trwgQ26xxx/LED_clock/FRAME/FRONT_STICKER/STICKER_CUT_3.pdf

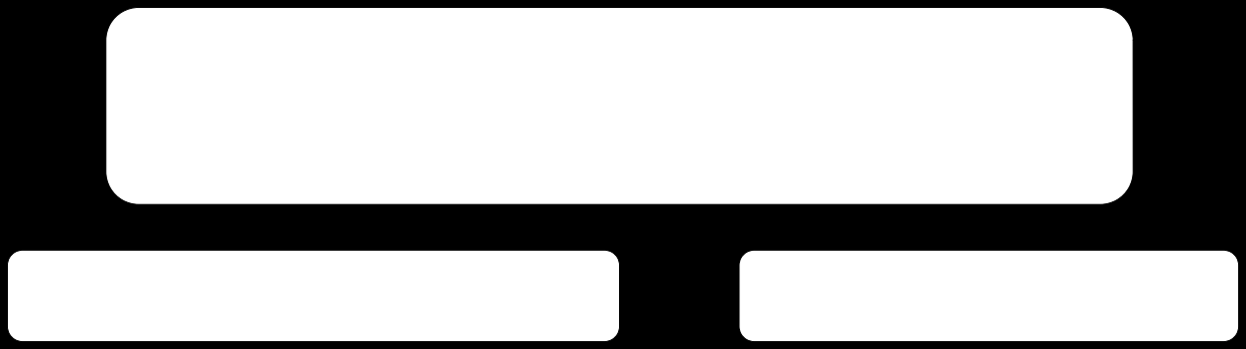
[picture p2: figure]
