trwgQ26xxx/LED_clock/FRAME/MOUNTING_PLATE/PLATE_WITH_DIMENSIONS.pdf

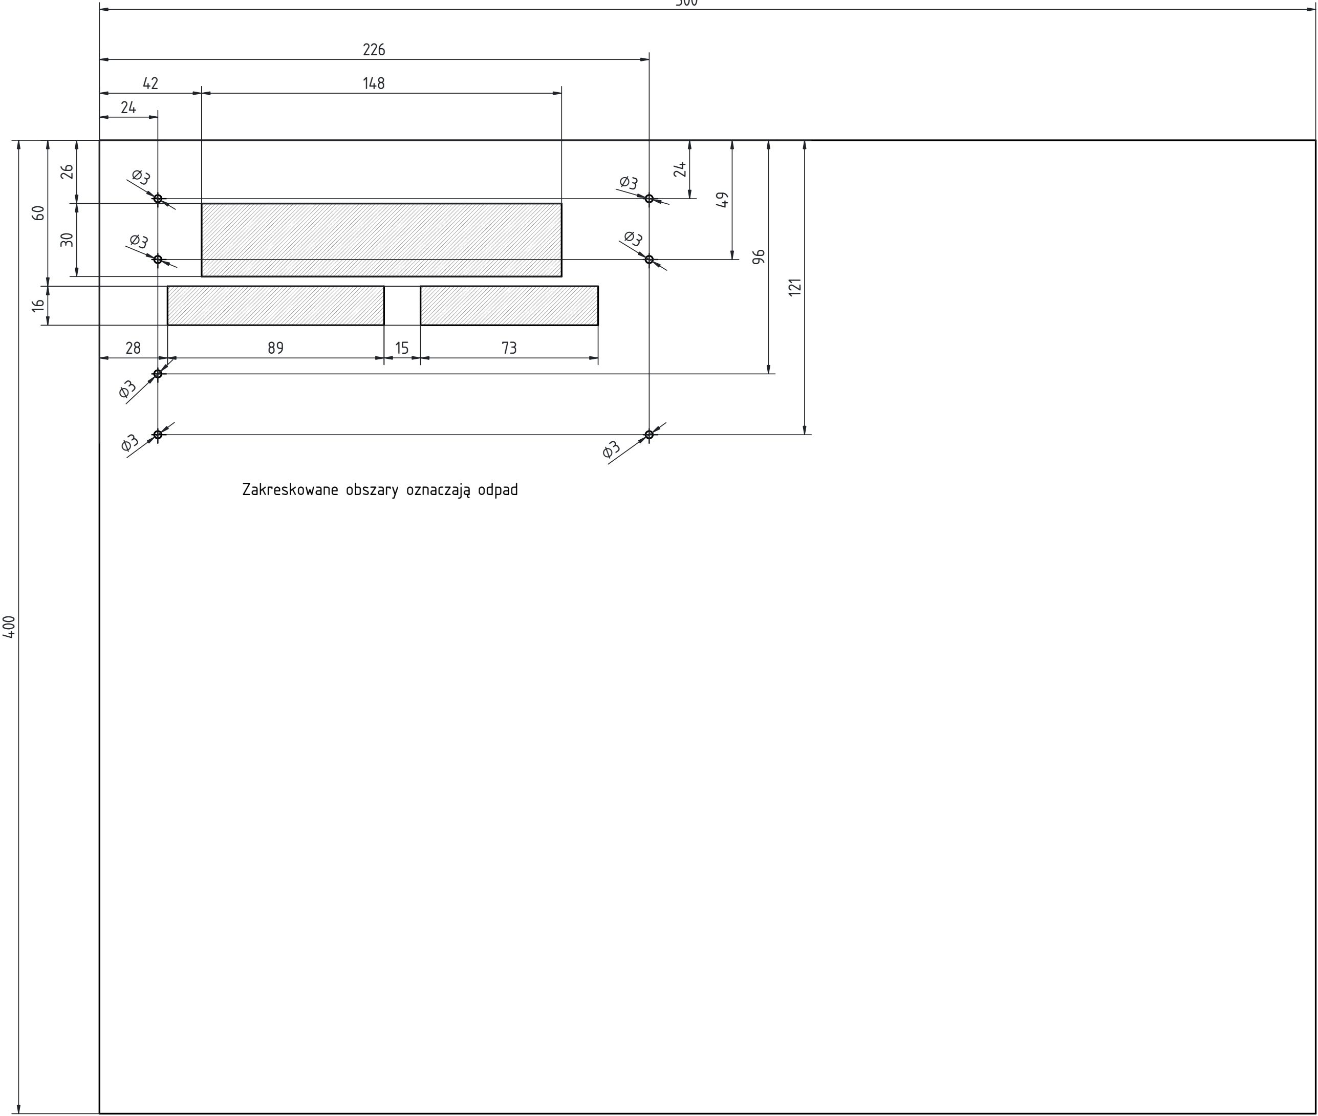
[picture p3: figure]
Zakreskowane obszary oznaczają odpad

500
