trwgQ26xxx/LED_clock/FRAME/MOUNTING_PLATE/PLATE_WITHOUT_DIMENSIONS.pdf

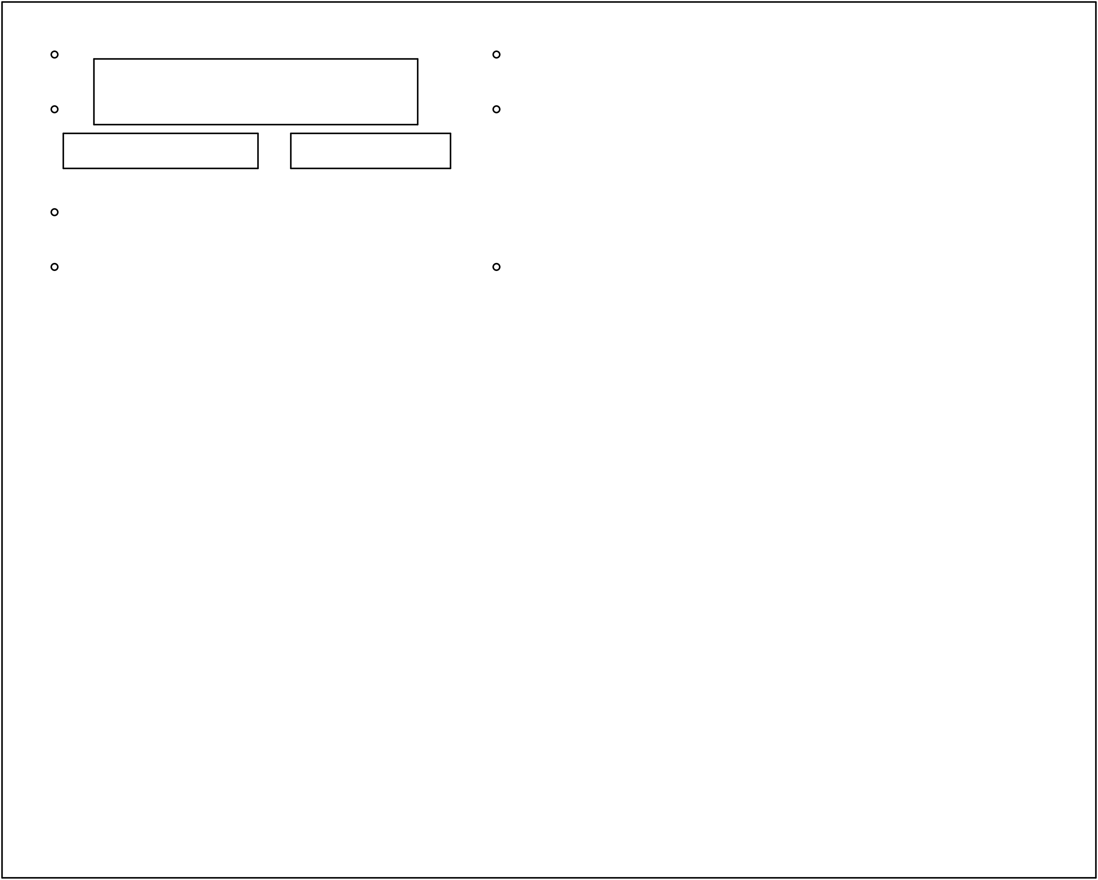
[picture p4: figure]
