trwgQ26xxx/LED_clock/firmware/clock/Clock/clock.h

/*
 * clock.h
 *
 *  Created on: Feb 8, 2025
 *      Author: trwgQ26xxx
 */

#ifndef CLOCK_H_
#define CLOCK_H_

void Set_update_display_flag(void);

void Init(void);

void Run(void);

#endif /* CLOCK_H_ */
