trwgQ26xxx/LED_clock/firmware/clock/Clock/rtc_drv.h

/*
 * rtc_drv.h
 *
 *  Created on: Feb 8, 2025
 *      Author: trwgQ26xxx
 */

#ifndef RTC_DRV_H_
#define RTC_DRV_H_

#include <stdint.h>

struct rtc_data_struct
{
	uint8_t year;
	uint8_t month;
	uint8_t date;
	uint8_t hour;
	uint8_t minute;
	uint8_t second;

	int8_t temperature;
};

uint8_t Init_RTC(void);

uint8_t Get_RTC_data(volatile struct rtc_data_struct *rtc_data);

uint8_t Set_RTC_time(volatile struct rtc_data_struct *rtc_data);

#endif /* RTC_DRV_H_ */
